counterbeing/liteswarm/src/Animation.h

#ifndef ANIMATION_H
#define ANIMATION_H
#include "config.h"
#include "FastLED.h"
#include "MyKnob.h"

class Animation
{
protected:
    int start;
    int finish;
    int initialSetting;
    unsigned long previousMillis = 0;
    bool initialized = false;

    int remapInRange(int index)
    {
        if (index < 0)
            return NUMPIXELS;
        if (index > NUMPIXELS)
            return 0;
        return index;
    }

    bool nonBlockDelay(unsigned int interval)
    {
        unsigned long current_millis = millis();
        if ((current_millis - previousMillis) > interval)
        {
            previousMillis = current_millis;
            return true;
        }
        return false;
    }
    virtual void loop() = 0;

public:
    virtual void setup() = 0;
    Animation(){};
    void run()
    {
        // if (!initialized)
        // {
        //     setup();
        //     initialized = true;
        // };
        loop();
    }
};
#endif
